zjywdq/elysia/elysia-voice-assistant/firmware/esp32-a2dp/main/bt_config.example.h

#pragma once
// Copy to bt_config.local.h to connect directly to your own headset.
// All zeroes: discover CONFIG_EXAMPLE_PEER_DEVICE_NAME from menuconfig.
#define APP_TARGET_PEER_BDA {0x00, 0x00, 0x00, 0x00, 0x00, 0x00}
